bitbank2/Pocket_CO2/User/Roboto_Black_13.h

// Created by http://oleddisplay.squix.ch/ Consider a donation
// In case of problems make sure that you are using the font file with the correct version!
const uint8_t Roboto_Black_13Bitmaps[] PROGMEM = {

	// Bitmap Data:
	0x00, // ' '
	0xFF,0xF3,0xC0, // '!'
	0xFF,0xBB, // '"'
	0x14,0x29,0xF9,0x62,0xDF,0xCA,0x14,0x68, // '#'
	0x11,0xEC,0xF3,0xE1,0xC1,0xF3,0xCD,0xE1,0x00, // '$'
	0xE0,0xB6,0xB4,0xE8,0x10,0x37,0x29,0x49,0x07, // '%'
	0x38,0x36,0x1B,0x0F,0x83,0xB3,0xDB,0xBC,0xDC,0x7F,0x80, // '&'
	0xFF, // '''
	0x27,0x4C,0xCC,0xCC,0xCC,0x46,0x30, // '('
	0x4E,0x23,0x33,0x33,0x33,0x26,0xC0, // ')'
	0x30,0x4F,0xCC,0x79,0x20, // '*'
	0x30,0x63,0xF9,0x83,0x00, // '+'
	0xFE, // ','
	0xF0, // '-'
	0xF0, // '.'
	0x19,0x8C,0x42,0x31,0x08,0xC4,0x00, // '/'
	0x7B,0x3C,0xF3,0xCF,0x3C,0xF3,0x78, // '0'
	0x3F,0x33,0x33,0x33,0x30, // '1'
	0x7B,0x3C,0xC3,0x18,0xE7,0x38,0xFC, // '2'
	0x7B,0x30,0xCE,0x0C,0x3C,0xF3,0x78, // '3'
	0x18,0xE3,0x9E,0xDB,0xF1,0x86,0x18, // '4'
	0xFF,0x0C,0x3E,0x4C,0x30,0xF3,0x78, // '5'
	0x39,0x8C,0x3E,0xCF,0x3C,0xF3,0x78, // '6'
	0xFE,0x0C,0x30,0x61,0x83,0x0E,0x18,0x70, // '7'
	0x7B,0x3C,0xDE,0xCF,0x3C,0xF3,0x78, // '8'
	0x38,0xC9,0x9F,0x36,0x67,0xC1,0x86,0x30, // '9'
	0xF0,0x3C, // ':'
	0xF0,0x3F,0x80, // ';'
	0x04,0xFF,0x3C,0x3C,0x10, // '<'
	0xFC,0x00,0x3F, // '='
	0x87,0x8E,0x7F,0x40, // '>'
	0x79,0xBE,0xC3,0x18,0xC0,0x0C,0x30, // '?'
	0x0F,0x86,0x18,0x81,0xA3,0x94,0x93,0xB2,0x76,0x4E,0xDB,0x4D,0xCC,0x00,0xC0,0x0F,0x80, // '@'
	0x1C,0x0E,0x0F,0x06,0xC3,0x63,0xF9,0x8C,0xC6,0xC3,0x80, // 'A'
	0xF9,0x9B,0x36,0x6F,0x99,0xF3,0xE6,0xFC, // 'B'
	0x3D,0x8F,0x1E,0x0C,0x18,0x31,0xE3,0x3C, // 'C'
	0xF9,0x9B,0x3E,0x3C,0x78,0xF3,0xE6,0xF8, // 'D'
	0xFF,0x0C,0x30,0xFB,0x0C,0x30,0xFC, // 'E'
	0xFF,0x0C,0x30,0xFF,0x0C,0x30,0xC0, // 'F'
	0x7D,0xCF,0x1E,0x0C,0xF8,0xF1,0xF3,0x3C, // 'G'
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
};
const GFXglyph Roboto_Black_13Glyphs[] PROGMEM = {
// bitmapOffset, width, height, xAdvance, xOffset, yOffset
	  {     0,   1,   1,   4,    0,   -1 }, // ' '
	  {     1,   2,   9,   5,    1,   -9 }, // '!'
	  {     4,   4,   4,   5,    0,  -10 }, // '"'
	  {     6,   7,   9,   9,    0,   -9 }, // '#'
	  {    14,   6,  11,   9,    1,  -10 }, // '$'
	  {    23,   8,   9,  11,    1,   -9 }, // '%'
	  {    32,   9,   9,  10,    0,   -9 }, // '&'
	  {    43,   2,   4,   3,    0,  -10 }, // '''
	  {    44,   4,  13,   6,    1,  -10 }, // '('
	  {    51,   4,  13,   6,    0,  -10 }, // ')'
	  {    58,   6,   6,   7,    0,   -9 }, // '*'
	  {    63,   7,   5,   8,    0,   -7 }, // '+'
	  {    68,   2,   4,   5,    1,   -2 }, // ','
	  {    69,   4,   1,   7,    1,   -5 }, // '-'
	  {    70,   2,   2,   5,    1,   -2 }, // '.'
	  {    71,   5,  10,   6,    0,   -9 }, // '/'
	  {    78,   6,   9,   9,    1,   -9 }, // '0'
	  {    85,   4,   9,   9,    1,   -9 }, // '1'
	  {    90,   6,   9,   9,    1,   -9 }, // '2'
	  {    97,   6,   9,   9,    1,   -9 }, // '3'
	  {   104,   6,   9,   9,    1,   -9 }, // '4'
	  {   111,   6,   9,   9,    1,   -9 }, // '5'
	  {   118,   6,   9,   9,    1,   -9 }, // '6'
	  {   125,   7,   9,   9,    0,   -9 }, // '7'
	  {   133,   6,   9,   9,    1,   -9 }, // '8'
	  {   140,   7,   9,   9,    0,   -9 }, // '9'
	  {   148,   2,   7,   5,    1,   -7 }, // ':'
	  {   150,   2,   9,   5,    1,   -7 }, // ';'
	  {   153,   6,   6,   8,    0,   -7 }, // '<'
	  {   158,   6,   4,   9,    1,   -6 }, // '='
	  {   161,   5,   6,   8,    1,   -7 }, // '>'
	  {   165,   6,   9,   8,    0,   -9 }, // '?'
	  {   172,  11,  12,  13,    0,   -9 }, // '@'
	  {   189,   9,   9,  10,    0,   -9 }, // 'A'
	  {   200,   7,   9,   9,    1,   -9 }, // 'B'
	  {   208,   7,   9,  10,    1,   -9 }, // 'C'
	  {   216,   7,   9,   9,    1,   -9 }, // 'D'
	  {   224,   6,   9,   8,    1,   -9 }, // 'E'
	  {   231,   6,   9,   8,    1,   -9 }, // 'F'
	  {   238,   7,   9,  10,    1,   -9 }, // 'G'
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
};
const GFXfont Roboto_Black_13 PROGMEM = {
(uint8_t  *)Roboto_Black_13Bitmaps,(GFXglyph *)Roboto_Black_13Glyphs,0x20, 0x7E, 17};
