bitbank2/Pocket_CO2/User/Arduino.h

//
// Arduino work-alike wrapper functions
// written by Larry Bank
// bitbank@pobox.com
// Copyright (c) 2023 BitBank Software, Inc.
//
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
#ifndef USER_ARDUINO_H_
#define USER_ARDUINO_H_

// GPIO pin states
enum {
	OUTPUT = 0,
	INPUT,
	INPUT_PULLUP,
	INPUT_PULLDOWN
};

#define PROGMEM
#define memcpy_P memcpy
#define pgm_read_byte(s) *(uint8_t *)s
#define pgm_read_word(s) *(uint16_t *)s

// Wrapper methods
void delay(int i);
//
// Digital pin functions use a numbering scheme to make it easier to map the
// pin number to a port name and number
// The GPIO ports A-D become the most significant nibble of the pin number
// for example, to use Port C pin 7 (C7), use the pin number 0xC7
//
void pinMode(uint8_t u8Pin, int iMode);
uint8_t digitalRead(uint8_t u8Pin);
void digitalWrite(uint8_t u8Pin, uint8_t u8Value);

// The Wire library is a C++ class; I've created a work-alike to my
// BitBang_I2C API which is a set of C functions to simplify I2C
void I2CInit(int iSpeed);
void I2CWrite(uint8_t u8Addr, uint8_t *pData, int iLen);
void I2CRead(uint8_t u8Addr, uint8_t *pData, int iLen);
int I2CTest(uint8_t u8Addr);
void I2CSetSpeed(int iSpeed);

// SPI1 (polling mode)
void SPI_write(uint8_t *pData, int iLen);
void SPI_begin(int iSpeed, int iMode);


// Random stuff
void Standby82ms(uint8_t iTicks);
void breatheLED(uint8_t u8Pin, int iPeriod);


#endif /* USER_ARDUINO_H_ */
